Sophi/messages/extras/globe v2 screenshots/Screenshot 2024-12-30 104841.png

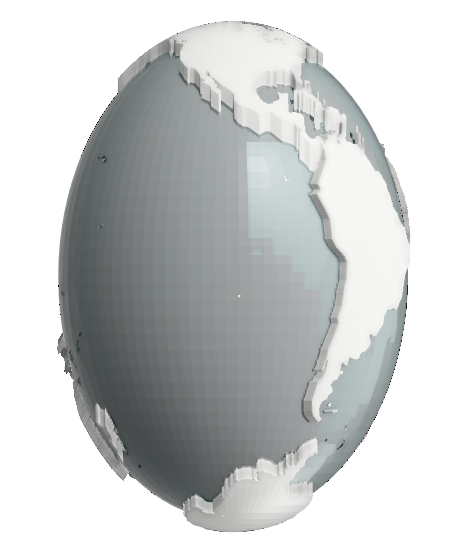
extras/globe v2 screenshots/Screenshot 2024-12-30 104841.png
