Sophi/messages/extras/globe v2 screenshots/Screenshot 2024-12-30 111803.png

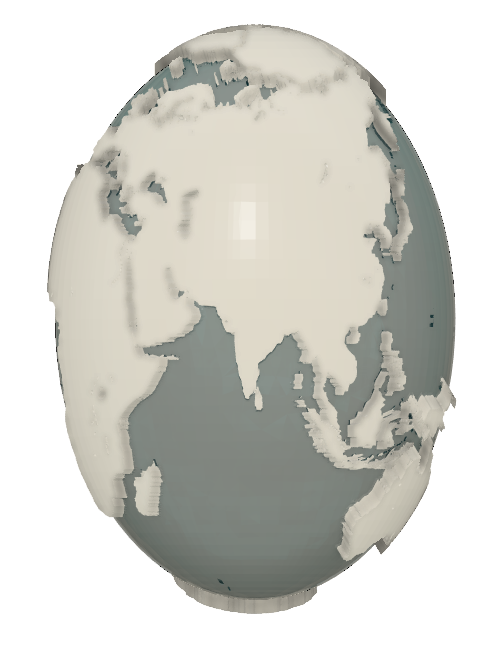
extras/globe v2 screenshots/Screenshot 2024-12-30 111803.png
